DreaM117er/Explorer-Keyboard-Blank/pic/spc/Resistor_THT.png

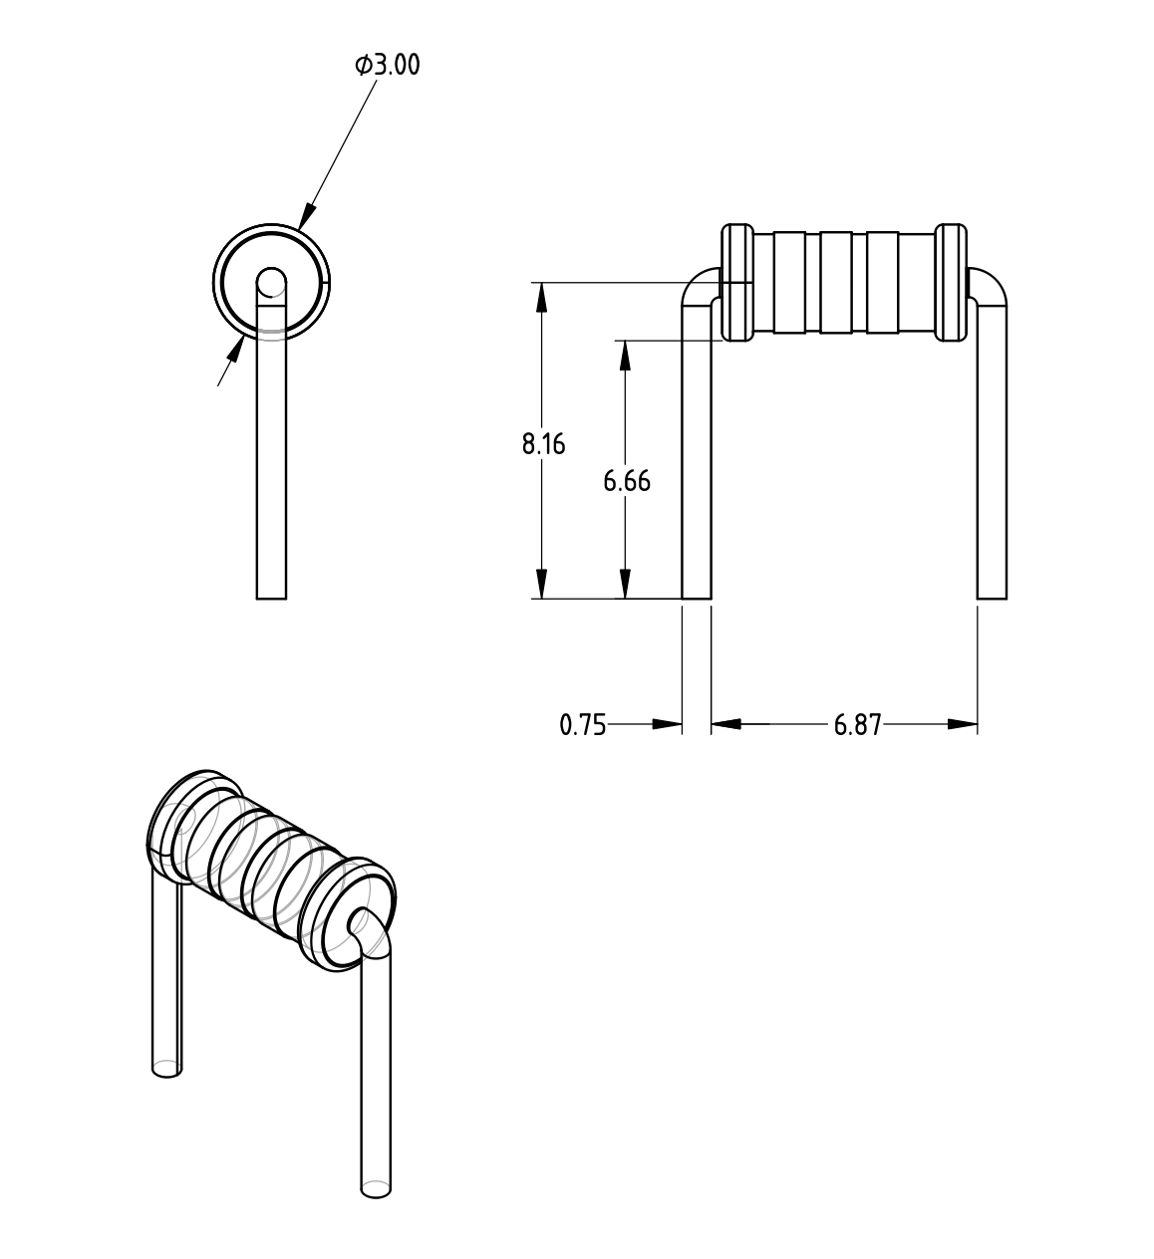
pic/spc/Resistor_THT.png
