DreaM117er/Explorer-Keyboard-Blank/file/pcb/v1/4x6/TPS/TPS.kicad_pcb

## KiCad design file/pcb/v1/4x6/TPS/TPS.kicad_pcb (2024-08-17, an earlier design)

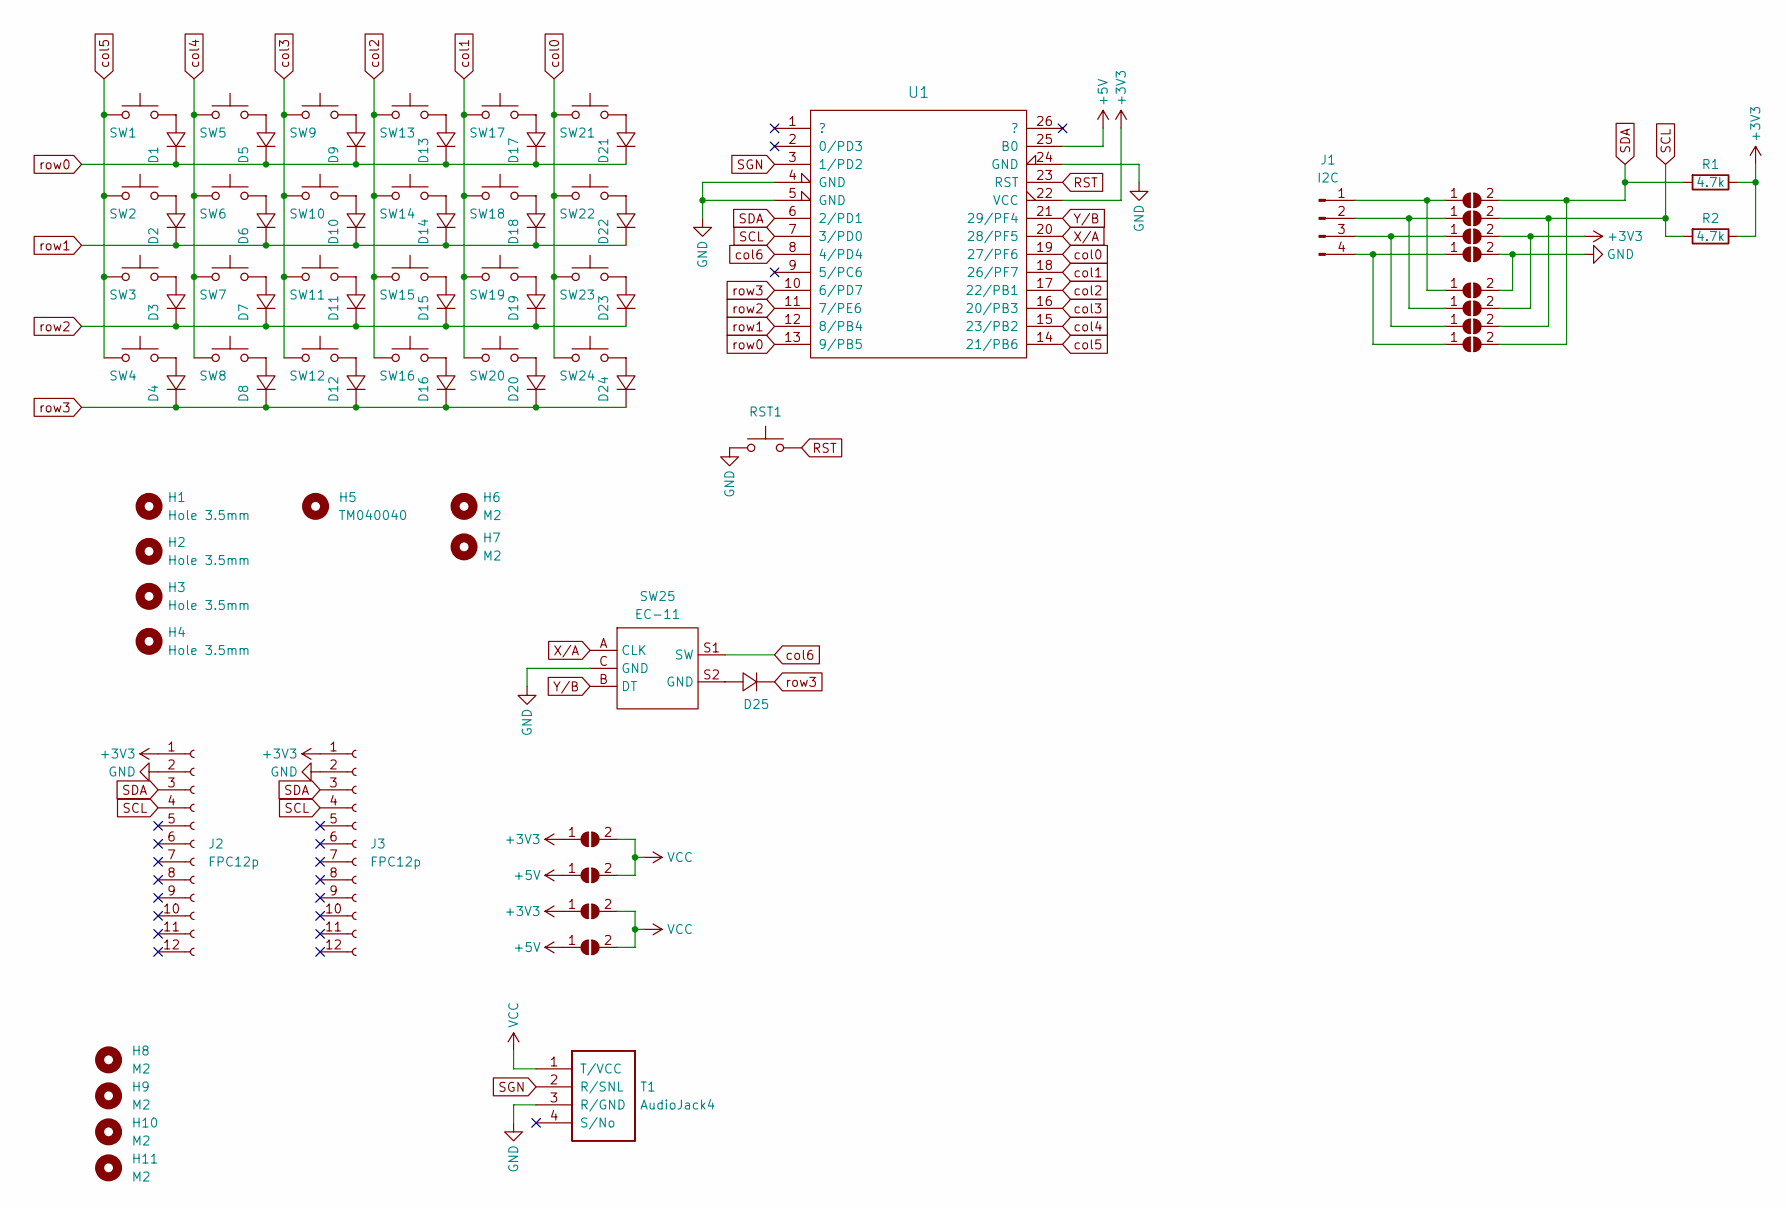
[picture p114: schematic TPS.kicad_sch]

Parts:
D1, D2, D3, D4, D5, D6, D7, D8, D9, D10, D11, D12, D13, D14, D15, D16, D17, D18, D19, D20, D21, D22, D23, D24, D25: 1N4148_SMD; D_SOD-123_dual
H1, H2, H3, H4: Hole 3.5mm; MountingHole_3.5mm
H5: TM040040; Trackpad_Cirque_TM040040
H6, H7, H8, H9, H10, H11: M2; MountingHole_2.2mm_M2
J1: I2C; PinHeader_1x04_P2.54mm_Vertical
J2, J3: FPC12p; Hirose_FH12-12S-0.5SH_1x12-1MP_P0.50mm_Horizontal
JP1, JP2, JP3, JP4: PWR1; SolderJumper-2_P1.3mm_Open_Pad1.0x1.5mm
JP5, JP6, JP7, JP8, JP9, JP10, JP11, JP12: PWR1; SolderJumper-2_P1.3mm_Open_RoundedPad1.0x1.5mm
R1, R2: 4.7k; R_Axial_DIN0204_L3.6mm_D1.6mm_P7.62mm_Horizontal
RST1: SW_Push; ResetSW_1side
SW1, SW2, SW3, SW4, SW5, SW6, SW7, SW8, SW9, SW10, SW11, SW12, SW13, SW14, SW15, SW16, SW17, SW18, SW19, SW20, SW21, SW22, SW23, SW24: SW_Push; SW_Choc_GLP_KLP12_Hotswap_1.00u_dual
SW25: EC-11; RotaryEncoder_EC11
T1: AudioJack4; TRRS-PJ-320A, dual side x2
U1: MCU_ProMicro_13p; MCU_ProMicro_13p_dual

Connections:
+3V3: J2.1, J3.1, JP1.1 (A), JP3.1 (A), JP7.2 (B), JP10.2 (B), R1.1, R2.1, U1.22 (VCC)
+5V: JP2.1 (A), JP4.1 (A), U1.25 (B0)
GND: J2.2, J3.2, JP8.2 (B), JP9.2 (B), RST1.1, SW25.C (GND), T1.3 (R/GND), U1.4 (GND), U1.5 (GND), U1.24 (GND)
unnamed: D1.2, SW1.2
unnamed: D2.2, SW2.2
unnamed: D3.2, SW3.2
unnamed: D4.2, SW4.2
unnamed: D5.2, SW5.2
unnamed: D6.2, SW6.2
unnamed: D7.2, SW7.2
unnamed: D8.2, SW8.2
unnamed: D9.2, SW9.2
unnamed: D10.2, SW10.2
unnamed: D11.2, SW11.2
unnamed: D12.2, SW12.2
unnamed: D13.2, SW13.2
unnamed: D14.2, SW14.2
unnamed: D15.2, SW15.2
unnamed: D16.2, SW16.2
unnamed: D17.2, SW17.2
unnamed: D18.2, SW18.2
unnamed: D19.2, SW19.2
unnamed: D20.2, SW20.2
unnamed: D21.2, SW21.2
unnamed: D22.2, SW22.2
unnamed: D23.2, SW23.2
unnamed: D24.2, SW24.2
unnamed: D25.2, SW25.S2 (GND)
unnamed: J1.1, JP5.1 (A), JP9.1 (A)
unnamed: J1.2, JP6.1 (A), JP10.1 (A)
unnamed: J1.3, JP7.1 (A), JP11.1 (A)
unnamed: J1.4, JP8.1 (A), JP12.1 (A)
RST: RST1.2, U1.23 (RST)
SCL: J2.4, J3.4, JP6.2 (B), JP11.2 (B), R2.2, U1.7 (3/PD0)
SDA: J2.3, J3.3, JP5.2 (B), JP12.2 (B), R1.2, U1.6 (2/PD1)
SGN: T1.2 (R/SNL), U1.3 (1/PD2)
VCC: JP1.2 (B), JP2.2 (B), JP3.2 (B), JP4.2 (B), T1.1 (T/VCC)
X/A: SW25.A (CLK), U1.20 (28/PF5)
Y/B: SW25.B (DT), U1.21 (29/PF4)
col0: SW21.1, SW22.1, SW23.1, SW24.1, U1.19 (27/PF6)
col1: SW17.1, SW18.1, SW19.1, SW20.1, U1.18 (26/PF7)
col2: SW13.1, SW14.1, SW15.1, SW16.1, U1.17 (22/PB1)
col3: SW9.1, SW10.1, SW11.1, SW12.1, U1.16 (20/PB3)
col4: SW5.1, SW6.1, SW7.1, SW8.1, U1.15 (23/PB2)
col5: SW1.1, SW2.1, SW3.1, SW4.1, U1.14 (21/PB6)
col6: SW25.S1 (SW), U1.8 (4/PD4)
row0: D1.1, D5.1, D9.1, D13.1, D17.1, D21.1, U1.13 (9/PB5)
row1: D2.1, D6.1, D10.1, D14.1, D18.1, D22.1, U1.12 (8/PB4)
row2: D3.1, D7.1, D11.1, D15.1, D19.1, D23.1, U1.11 (7/PE6)
row3: D4.1, D8.1, D12.1, D16.1, D20.1, D24.1, D25.1, U1.10 (6/PD7)

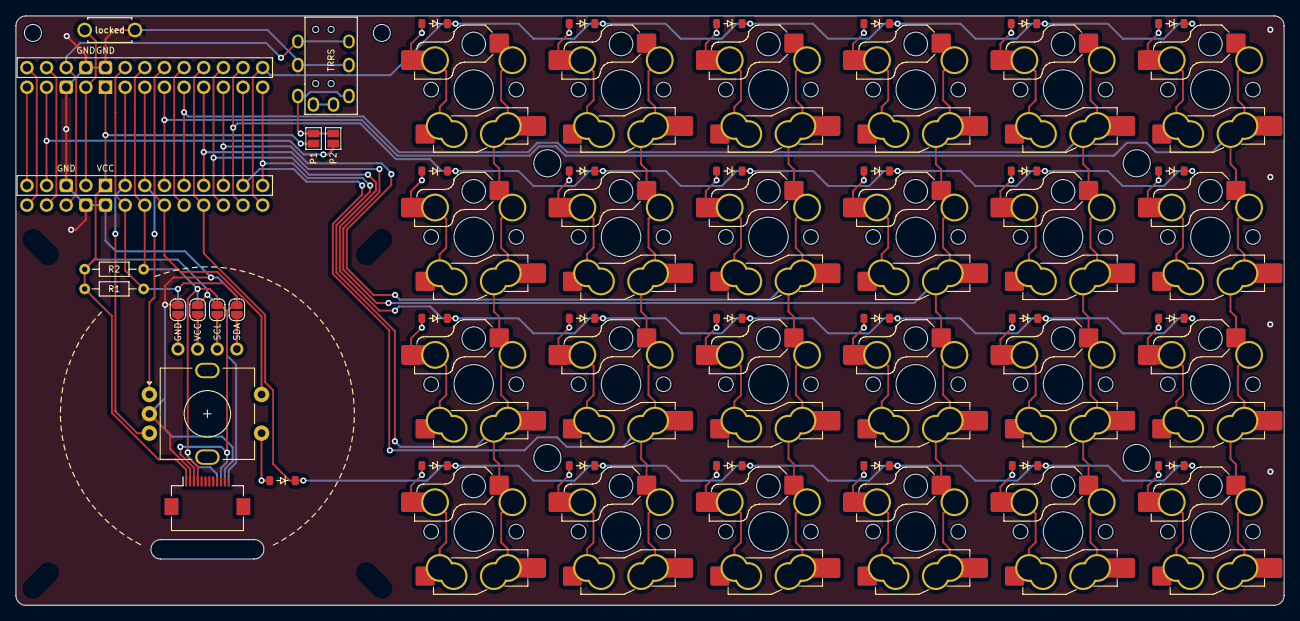
[picture p115: board file/pcb/v1/4x6/TPS/TPS.kicad_pcb from above]

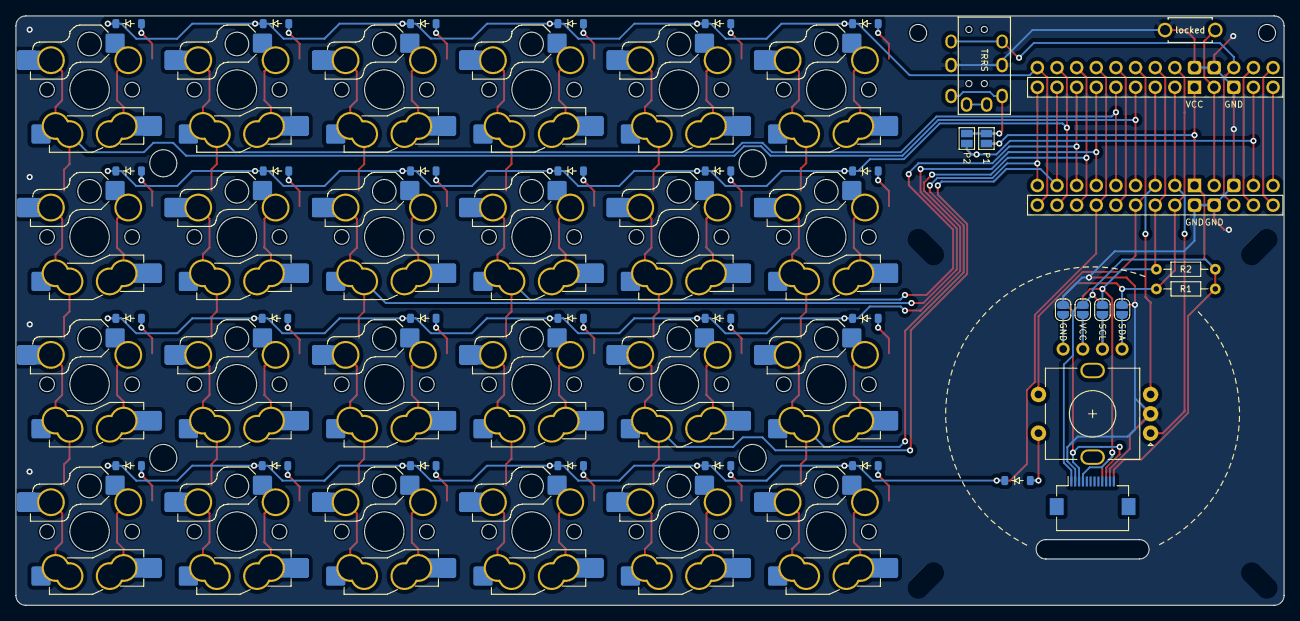
[picture p116: board file/pcb/v1/4x6/TPS/TPS.kicad_pcb from below]

Board: 2 copper layers, 164.0 x 76.2 mm, 81 parts (8 on the bottom side), 50 nets.
